Ruud14/DIY-Wifi-LEDStrip-Controller/to_ESP32/boot.py

import esp
esp.osdebug(None)
import network
import gc
import socket
import time
import os

ap_if = network.WLAN(network.AP_IF)
sta_if = network.WLAN(network.STA_IF)
DATA_PORT = 7777
connection_timeout = 60
ip_addr = ""
CONFIGURATION_SAVE_FILE = "configurations.save"
NETWORK_CONFIGURATION_SAVE_FILE = "netconfig.txt"


def save_network(ssid, password, hostname):
    with open(NETWORK_CONFIGURATION_SAVE_FILE, 'w') as f:
        f.write(",".join([ssid, password, hostname]))


def get_network():
    with open(NETWORK_CONFIGURATION_SAVE_FILE, 'r') as f:
        ssid, password, hostname = f.read().split(',')
        return ssid, password, hostname


def setup_network():
    gc.collect()
    if sta_if.isconnected():
        print("already connected")
        ap_if.active(False)
    else:
        sta_if.active(True)
        ap_if.active(True)
        sta_if.active(True)
        ap_if.config(essid="LedStrip Setup", password="Ruud14_LedStrip")
        s = socket.socket()
        s.bind(("0.0.0.0", DATA_PORT))
        s.listen(3)
        while True:
            client, addr = s.accept()
            print(addr, "connected")
            data = client.recv(1024).decode()
            ssid, password, hostname = data.split(",")
            if connect(ssid, password, hostname):
                client.send(ip_addr.encode())
                time.sleep(5)
                client.close()
                s.close()
                ap_if.active(False)
                save_network(ssid, password, hostname)
                break
            else:
                client.send("failed".encode())
                client.close()


def connect(ssid, password, host):
    global ip_addr
    try:
        sta_if.active(True)
        sta_if.config(dhcp_hostname=host)
        print('connecting to ',ssid,":",password)
        sta_if.active(True)
        sta_if.connect(ssid, password)
        total_time = 0
        while not sta_if.isconnected():
            if total_time > connection_timeout:
                print("Connecting to", ssid, "failed...")
                return False
            time.sleep(0.5)
            total_time+=0.5
        print('network config:', sta_if.ifconfig())
        ip_addr = sta_if.ifconfig()[0]
        return True
    except Exception as e:
        print(e)
        print("Connecting to", ssid, "failed...")
        return False


if __name__ == '__main__':
    time.sleep(3)
    try:
        ssid, password, hostname = get_network()
        if not connect(ssid, password, hostname):
            os.remove(CONFIGURATION_SAVE_FILE)
            setup_network()
    except OSError:
        setup_network()
    gc.collect()
